feer9/Tiny-thermometer/case/img2.jpg

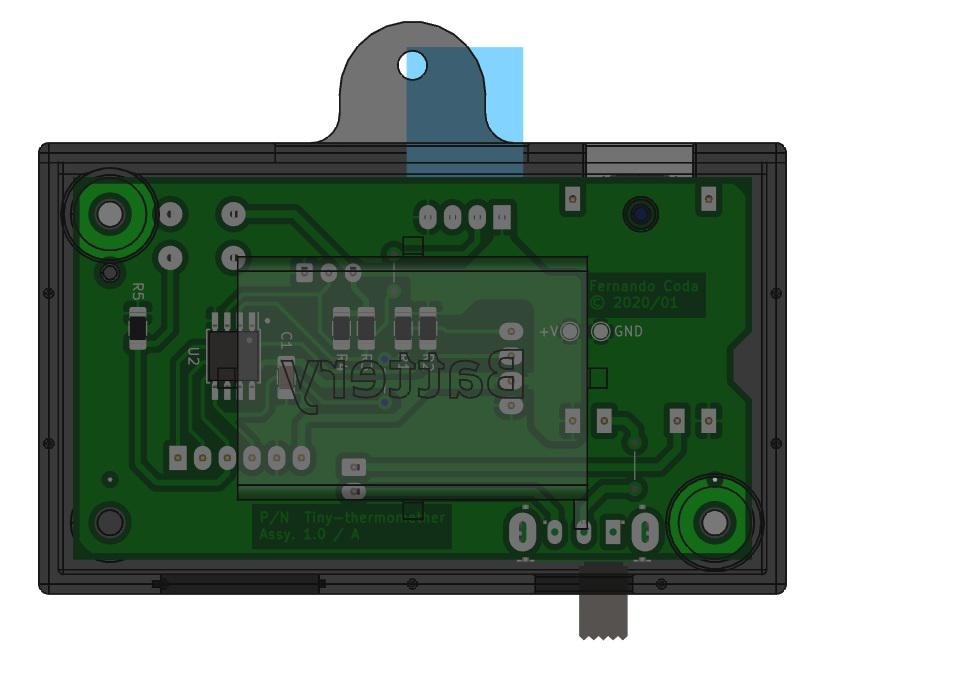
case/img2.jpg
