feer9/Tiny-thermometer/pcb/doc/img1.jpg

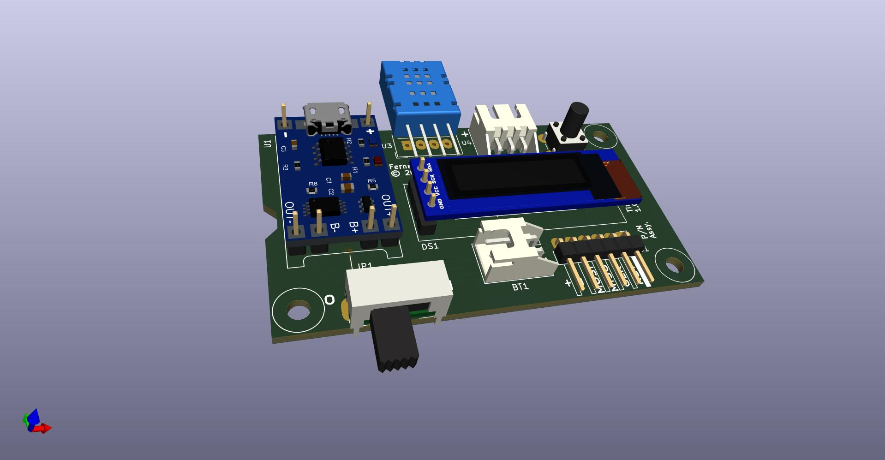
pcb/doc/img1.jpg
