feer9/Tiny-thermometer/pcb/doc/img2.jpg

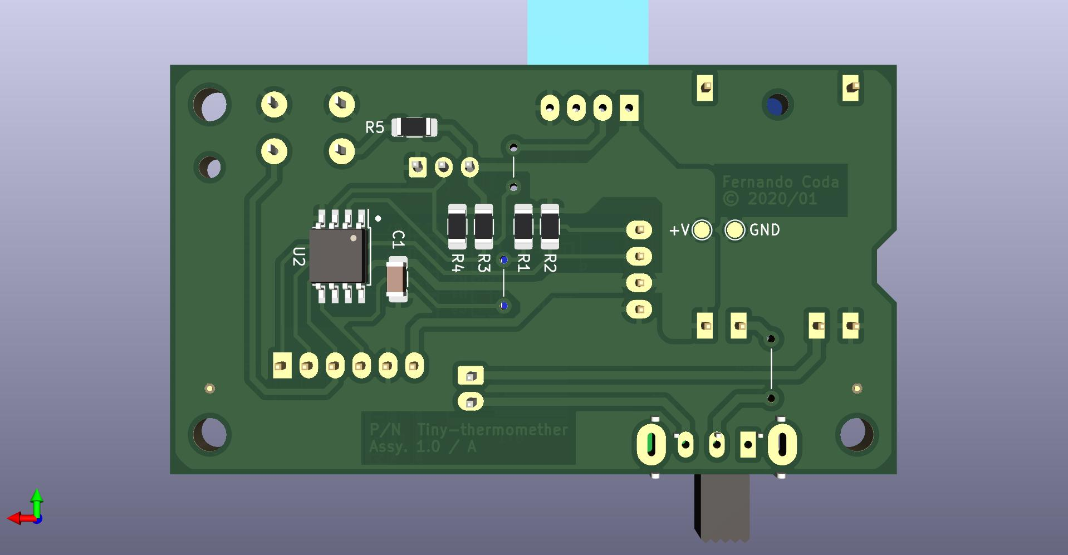
pcb/doc/img2.jpg
