feer9/Tiny-thermometer/src/bitmaps.c

#include "bitmaps.h"


// byte array of bitmap 10x32px
const uint8_t  img_thermometer_cold[] PROGMEM = {
	10,32,
	0x00, 0x00, 0xf0, 0x0c, 0x02, 0x02, 0x0c, 0xf0, 0x20, 0x20, 
	0x00, 0x00, 0xff, 0x00, 0x00, 0x00, 0x00, 0xff, 0x49, 0x49, 
	0x00, 0x80, 0xff, 0x00, 0x00, 0x00, 0x00, 0xff, 0x92, 0x12, 
	0x1e, 0x61, 0x40, 0x80, 0x80, 0x80, 0x80, 0x40, 0x61, 0x1e
};

// byte array of bitmap 10x32px
const uint8_t  img_thermometer_warm[] PROGMEM = {
	10,32,
	0x00, 0x00, 0xf0, 0x0c, 0x02, 0x02, 0x0c, 0xf0, 0x20, 0x20, 
	0x00, 0x00, 0xff, 0x00, 0x00, 0x00, 0x00, 0xff, 0x49, 0x49, 
	0x00, 0x80, 0xff, 0xfc, 0xfc, 0xfc, 0xfc, 0xff, 0x92, 0x12, 
	0x1e, 0x7f, 0x7f, 0xff, 0xff, 0xff, 0xff, 0x7f, 0x7f, 0x1e
};

// byte array of bitmap 10x32px
const uint8_t  img_thermometer_hot[] PROGMEM = {
	10,32,
	0x00, 0x00, 0xf0, 0xcc, 0xc2, 0xc2, 0xcc, 0xf0, 0x20, 0x20, 
	0x00, 0x00, 0xff, 0xff, 0xff, 0xff, 0xff, 0xff, 0x49, 0x49, 
	0x00, 0x80, 0xff, 0xff, 0xff, 0xff, 0xff, 0xff, 0x92, 0x12, 
	0x1e, 0x7f, 0x7f, 0xff, 0xff, 0xff, 0xff, 0x7f, 0x7f, 0x1e
};

// byte array of bitmap 23x32px
const uint8_t img_raindrop[94] PROGMEM = {
	23,32,
	0x00, 0x00, 0x00, 0x00, 0x00, 0x00, 0xc0, 0xf0, 0xf8, 0xfe, 0xff, 0xfc, 0xf0, 0xc0, 0x00, 0x00, 0x00, 0x00, 0x00, 0x00, 0x00, 0x00, 0x00, 
	0x00, 0x00, 0xe0, 0xf8, 0xfe, 0xff, 0xff, 0xff, 0xff, 0xff, 0xff, 0xff, 0xff, 0xff, 0xff, 0xfe, 0xfc, 0xf8, 0xf0, 0xe0, 0x80, 0x00, 0x00, 
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
 };
