feer9/Tiny-thermometer/include/bitmaps.h

#ifndef _BITMAPS_H
#define _BITMAPS_H

#include <stdint.h>
#include <avr/pgmspace.h>

extern const uint8_t img_thermometer_cold[] PROGMEM;
extern const uint8_t img_thermometer_warm[] PROGMEM;
extern const uint8_t img_thermometer_hot[] PROGMEM;
extern const uint8_t img_raindrop[] PROGMEM;

// Font structure as saved in flash memory
typedef struct {
  uint8_t type;
  uint8_t width;
  uint8_t height;
  uint8_t first_char;
  uint8_t data;
} font_t;

// Current font settings stored in SRAM
typedef struct {
  uint8_t width;
  uint8_t height;
  uint8_t first_char;
  uint16_t charSize;
  const uint8_t *data; // pointer to font_t[4], where actual characters start
} fontSettings;

// Fonts
extern const uint8_t ssd1306xled_font5x7_AB[] PROGMEM;
extern const uint8_t comic_sans_font24x32_123[] PROGMEM;
extern const uint8_t ssd1306xled_font8x16[] PROGMEM;
extern const uint8_t CantarellExtraBold_12x16[] PROGMEM;



#endif // _BITMAPS_H
